MariusS16/e-book-reader/Images/image.png

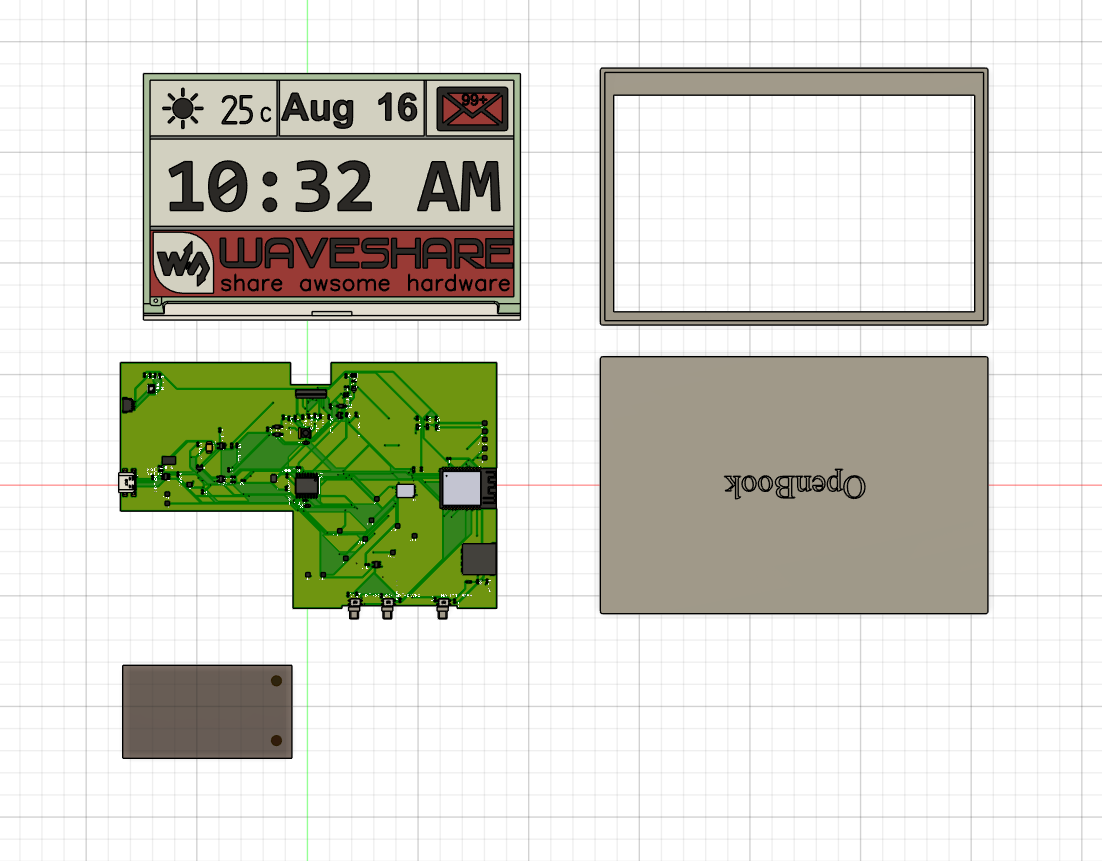
Images/image.png
