MariusS16/e-book-reader/Images/img1.jpg

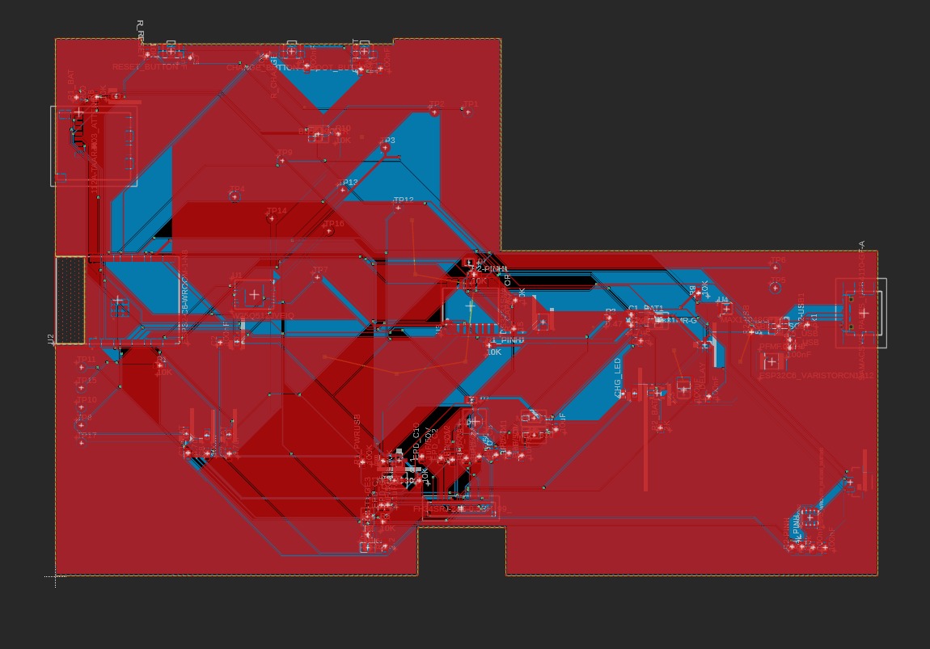
Images/img1.jpg
