MariusS16/e-book-reader/Images/img2.jpg

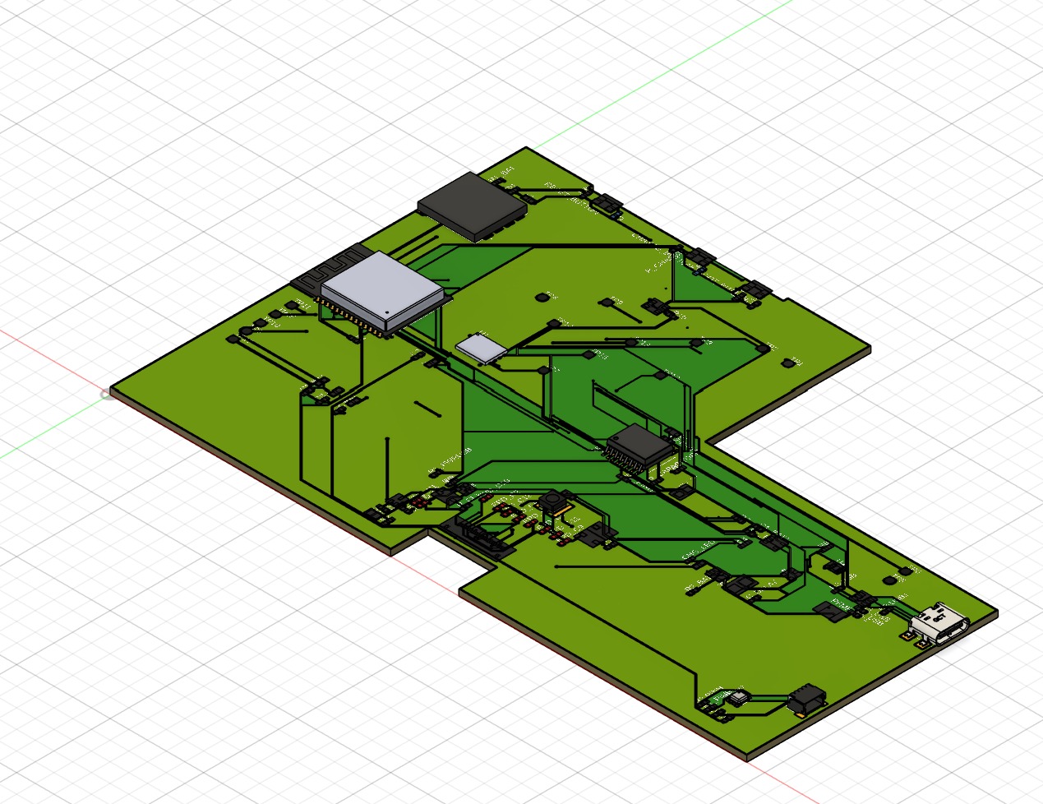
Images/img2.jpg
