MariusS16/e-book-reader/Images/img3.jpg

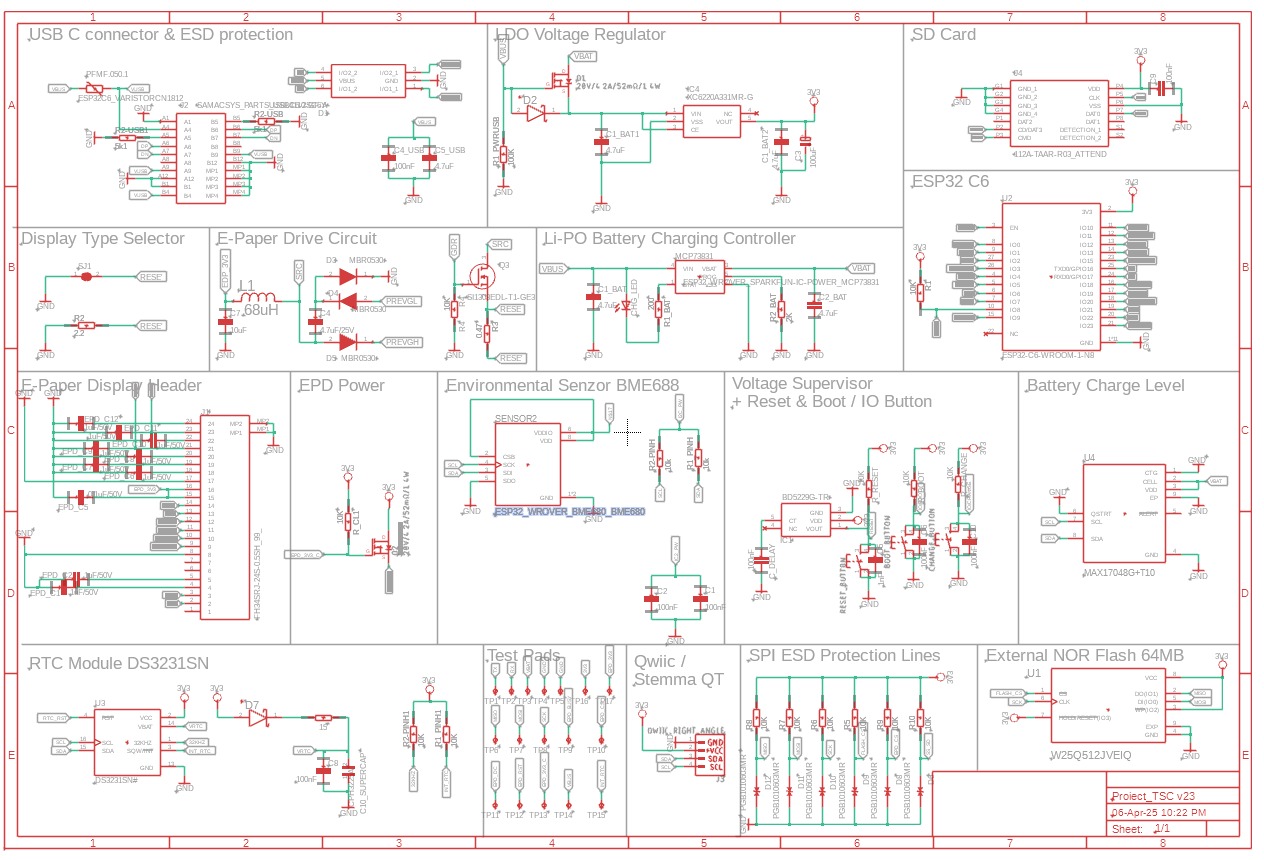
Images/img3.jpg
